webbdrew20-cmd/The_Beacon/s3_wroom_beacon/main/wifi_sta.c

#include "wifi_sta.h"
#include "wroom2_config.h"
#include <string.h>
#include "esp_log.h"
#include "esp_wifi.h"
#include "esp_event.h"
#include "esp_netif.h"

static const char *TAG = "wifi";

static void on_wifi_event(void *arg, esp_event_base_t base, int32_t id, void *data)
{
    if (base == WIFI_EVENT && id == WIFI_EVENT_STA_START) {
        esp_wifi_connect();
    } else if (base == WIFI_EVENT && id == WIFI_EVENT_STA_DISCONNECTED) {
        ESP_LOGW(TAG, "disconnected from \"%s\" — retrying", BEACON_SSID);
        vTaskDelay(pdMS_TO_TICKS(1000));
        esp_wifi_connect();
    } else if (base == IP_EVENT && id == IP_EVENT_STA_GOT_IP) {
        ESP_LOGI(TAG, "joined \"%s\" as %s", BEACON_SSID, W2_IP);
    }
}

esp_err_t wifi_sta_start(void)
{
    ESP_ERROR_CHECK(esp_netif_init());
    ESP_ERROR_CHECK(esp_event_loop_create_default());
    esp_netif_t *sta = esp_netif_create_default_wifi_sta();

    // Static IP: stop the DHCP client, set our address directly.
    esp_netif_dhcpc_stop(sta);
    esp_netif_ip_info_t ip = { 0 };
    ip.ip.addr = esp_ip4addr_aton(W2_IP);
    ip.gw.addr = esp_ip4addr_aton(W2_GATEWAY);
    ip.netmask.addr = esp_ip4addr_aton(W2_NETMASK);
    ESP_ERROR_CHECK(esp_netif_set_ip_info(sta, &ip));

    wifi_init_config_t icfg = WIFI_INIT_CONFIG_DEFAULT();
    ESP_ERROR_CHECK(esp_wifi_init(&icfg));
    ESP_ERROR_CHECK(esp_event_handler_register(WIFI_EVENT, ESP_EVENT_ANY_ID, on_wifi_event, NULL));
    ESP_ERROR_CHECK(esp_event_handler_register(IP_EVENT, IP_EVENT_STA_GOT_IP, on_wifi_event, NULL));

    wifi_config_t wc = { 0 };
    strlcpy((char *)wc.sta.ssid, BEACON_SSID, sizeof(wc.sta.ssid));
    if (strlen(BEACON_PASS)) {
        strlcpy((char *)wc.sta.password, BEACON_PASS, sizeof(wc.sta.password));
    }
    wc.sta.threshold.authmode = strlen(BEACON_PASS) ? WIFI_AUTH_WPA2_PSK : WIFI_AUTH_OPEN;

    ESP_ERROR_CHECK(esp_wifi_set_mode(WIFI_MODE_STA));
    ESP_ERROR_CHECK(esp_wifi_set_config(WIFI_IF_STA, &wc));
    ESP_ERROR_CHECK(esp_wifi_start());
    return ESP_OK;
}
